32teeth/VoltageConverters/images/IMG_0040.jpeg

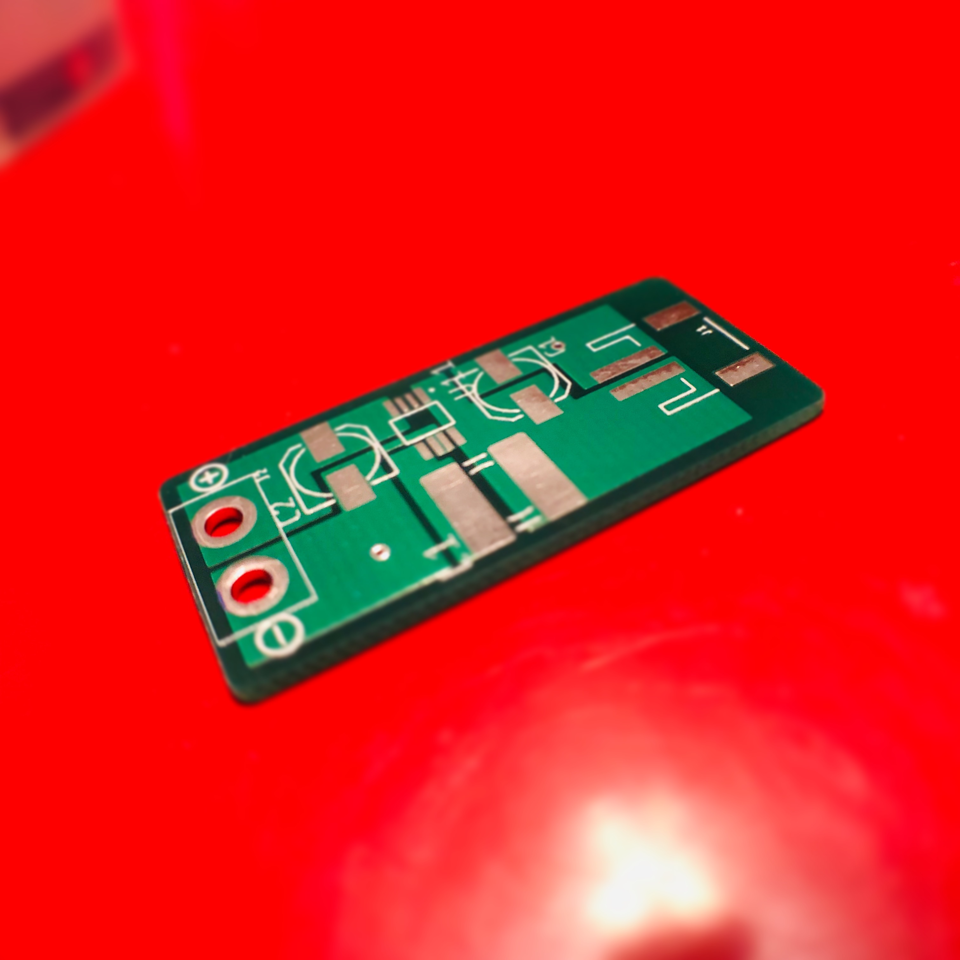
images/IMG_0040.jpeg
