32teeth/VoltageConverters/images/IMG_5226.jpeg

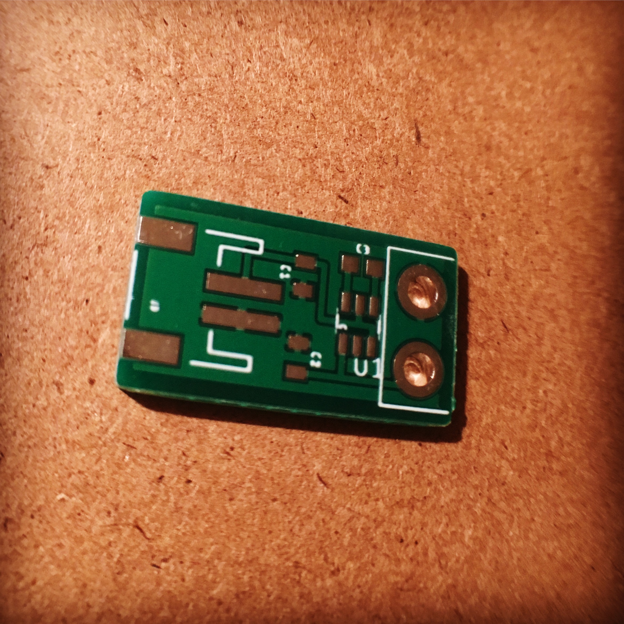
images/IMG_5226.jpeg
