32teeth/VoltageConverters/images/IMG_5315.jpeg

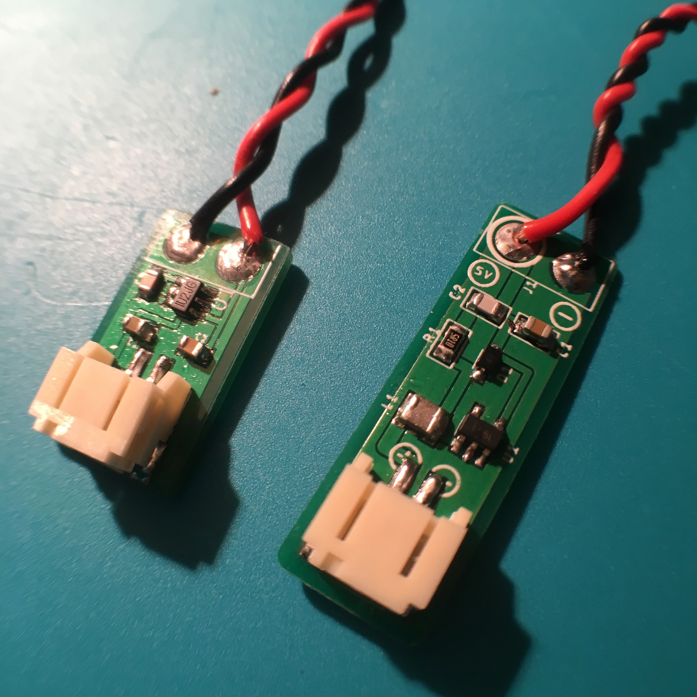
images/IMG_5315.jpeg
